jmmourier/laughing-couscous/software/applications/couscous/src/CouscousManager.cpp

#include "CouscousManager.h"

#include <atomic>
#include <chrono>
#include <cmath>

#include "Action.h"
#include "IHali.h"
#include "IHaliListener.h"
#include "Posi.h"
#include "PositionOrientation.h"
#include "RobotState.h"

CouscousManager::CouscousManager(
    const std::shared_ptr<IHali> &hali,
    const std::shared_ptr<Posi> &posi,
    const std::shared_ptr<WebServer> &web_server,
    const std::shared_ptr<Navi> &navi,
    const std::shared_ptr<Missi> &missi)
    : hali_(hali),
      posi_(posi),
      navi_(navi),
      web_server_(web_server),
      missi_(missi),
      is_robot_ready_(false),
      pre_launch_test_done_(false),
      mission_finished_(false) {
    web_server_thread_ = std::thread([&] { web_server_->start(); });

    // this is temporary and shall be replaced by a a listener on the strart button on the robot
    missi_->actionHasBeenDone();
}

void CouscousManager::runPreLaunchTest() {
    std::this_thread::sleep_for(std::chrono::milliseconds(1000));
    hali_->setGrabber(GrabberState::grabberClose);
    std::this_thread::sleep_for(std::chrono::milliseconds(1000));
    hali_->setGrabber(GrabberState::grabberOpen);
    std::this_thread::sleep_for(std::chrono::milliseconds(1000));
}

void CouscousManager::onPositionChanged(const PositionOrientation &position_orientation) {
    if (!pre_launch_test_done_ || !is_robot_ready_) {
        return;
    }
    RobotState currentState = web_server_->getRobotState();

    navi_->setCurrentPosition(
        position_orientation.x_m_,
        position_orientation.y_m_,
        position_orientation.orientation_rad_);

    Action nextAction = missi_->getCurrentAction();
    web_server_->setRobotState(RobotState(
        position_orientation,
        currentState.battery_,
        currentState.is_grabber_open_,
        currentState.mission_started_at_,
        currentState.mission_ended_at_,
        nextAction.type));

    if (nextAction.arguments == "mission done" && mission_finished_ == false) {
        const auto now = std::chrono::system_clock::now();
        const auto end_mission_timestamp =
            std::chrono::duration_cast<std::chrono::seconds>(now.time_since_epoch()).count();

        web_server_->setRobotState(RobotState(
            currentState.position_orientation_,
            currentState.battery_,
            currentState.is_grabber_open_,
            currentState.mission_started_at_,
            end_mission_timestamp,
            currentState.current_action_));
        mission_finished_ = true;
    }

    if (nextAction.type == WAIT) {
        std::cout << "[Missi]:wait" << std::endl;
        // wait timeout or mission is not started or mission is done
    } else if (nextAction.type == MOVE) {
        std::cout << "[Missi]:move" << nextAction.target_x << " " << nextAction.target_y
                  << std::endl;
        if (!nextAction.hasActionStarted) {
            navi_->setTargetPosition(nextAction.target_x, nextAction.target_y, 0);
        }
    } else if (nextAction.type == GRABBER) {
        std::cout << "[Missi]:grabber  : " << nextAction.grabber_state << std::endl;
        // define how this is read
        IHaliListener::GrabberState grabber_state = (nextAction.grabber_state.compare("open") == 0)
                                                        ? IHaliListener::GrabberState::grabberOpen
                                                        : IHaliListener::GrabberState::grabberClose;
        if (hali_->getGrabber() != grabber_state) {
            hali_->setGrabber(grabber_state);
        }
    } else if (nextAction.type == TURN) {
        std::cout << "[Missi]:turning " << nextAction.angle << std::endl;
        // TODO this need to be implemented
        if (!nextAction.hasActionStarted) {
            navi_->setTargetOrientation(nextAction.angle);
        }
    } else if (nextAction.type == MOVE_BACKWARD) {
        std::cout << "[Missi]:moving backward: " << nextAction.backward_distance << std::endl;
        if (!nextAction.hasActionStarted) {
            navi_->setBackwardDistance(nextAction.backward_distance);
        }
    } else if (nextAction.type == MOVE_FORWARD) {
        std::cout << "[Missi]:moving forward: " << nextAction.forward_distance << std::endl;
        if (!nextAction.hasActionStarted) {
            navi_->setForwardDistance(nextAction.forward_distance);
        }
    } else if (nextAction.type == UNKNOWN) {
        std::cout << "[Missi]:unknow action" << missi_->actionTypeToString(nextAction.type)
                  << std::endl;
        // This is abnormal, let's skip to next action
        missi_->actionHasBeenDone();
    }

    nextAction.hasActionStarted = true;
}

void CouscousManager::onWebServerPositionRequest(const PositionOrientation &position_orientation) {
    posi_->setPosition(position_orientation);
}

void CouscousManager::onWebServerSpeedRequest(const int &speed_motor1, const int &speed_motor2) {
    std::cout << "speed" << speed_motor1 << " " << speed_motor2 << std::endl;
    hali_->setMd25Speed(speed_motor1, speed_motor2);
}

// webserver send target position
void CouscousManager::onWebServerTargetPositionRequest(const double &pos_x, const double &pos_y) {
    navi_->setTargetPosition(pos_x, pos_y, 0);
}

// webserver send target rotation
void CouscousManager::onWebServerTargetOrientationRequest(const float &orientation_rad) {
    navi_->setTargetOrientation(orientation_rad);
};

void CouscousManager::onGrabberStateChanged(const GrabberState &graberState) {
    RobotState currentState = web_server_->getRobotState();
    web_server_->setRobotState(RobotState(
        currentState.position_orientation_,
        currentState.battery_,
        graberState == GrabberState::grabberOpen,
        currentState.mission_started_at_,
        currentState.mission_ended_at_,
        currentState.current_action_));
};

void CouscousManager::onNaviTargetReachedRequest(void) {
    Action current_action = missi_->getCurrentAction();
    if (current_action.type == MOVE || current_action.type == TURN ||
        current_action.type == MOVE_BACKWARD || current_action.type == MOVE_FORWARD) {
        missi_->actionHasBeenDone();
    }
}

// void CouscousManager::onNaviSpeedRequest(const int &speed_motor1, const int &speed_motor2) {
void CouscousManager::onNaviSpeedRequest(
    const float &v_x_mps,
    const float &v_y_mps,
    const float &omega_radps) {
    MotorSpeed motor_speed =
        moti_.getMotorSpeedFromBaseSpeed(BaseSpeed(v_x_mps, v_y_mps, omega_radps));
    hali_->setMd25Speed(motor_speed.speed_motor_1_, motor_speed.speed_motor_2_);
}

void CouscousManager::start() {
    hali_thread_ = std::thread([&] { hali_->updater(); });

    long rounds = 0;

    while (true) {
        if (is_robot_ready_) {
            auto encoders_motor1 = hali_->getEncoder(MotorIdEnum::motor1);
            auto encoders_motor2 = hali_->getEncoder(MotorIdEnum::motor2);

            posi_->updatePosition(encoders_motor1, encoders_motor2);

            if (rounds % (INTERVAL_REFRESH_BATTERY_MS / INTERVAL_REFRESH_MS) == 0) {
                RobotState currentState = web_server_->getRobotState();
                web_server_->setRobotState(RobotState(
                    currentState.position_orientation_,
                    static_cast<float>(hali_->getBatteryVoltage()) / 10,
                    currentState.is_grabber_open_,
                    currentState.mission_started_at_,
                    currentState.mission_ended_at_,
                    currentState.current_action_));
            }

            rounds++;
        } else if (!pre_launch_test_done_) {
            runPreLaunchTest();
            pre_launch_test_done_ = true;
        } else if (pre_launch_test_done_ && hali_->isRobotStarted()) {
            IHaliListener::RobotColor robot_color =
                hali_->getSwitch(SwitchId::switch1) ? RobotColor::YELLOW : RobotColor::BLUE;

            // Setting mission file according to robot's color
            std::string mission_file = std::string(std::getenv("MISSION_PATH")).append("/");
            missi_->setMissionFilePath(
                robot_color == RobotColor::YELLOW ? mission_file.append("mission_yellow.json")
                                                  : mission_file.append("mission_blue.json"));

            // note : the file mission.json shall be present on the same path the app is executed
            missi_->loadMissionFile();

            // Setting starting position according to robot's color
            auto starting_position = robot_color == RobotColor::YELLOW
                                         ? PositionOrientation(2.8, 1.2, M_PI)
                                         : PositionOrientation(0.2, 1.2, 0);

            const auto now = std::chrono::system_clock::now();
            const auto start_mission_timestamp =
                std::chrono::duration_cast<std::chrono::seconds>(now.time_since_epoch()).count();

            RobotState currentState = web_server_->getRobotState();
            web_server_->setRobotState(RobotState(
                currentState.position_orientation_,
                currentState.battery_,
                currentState.is_grabber_open_,
                start_mission_timestamp,
                currentState.mission_ended_at_,
                currentState.current_action_));

            posi_->setPosition(starting_position);

            is_robot_ready_ = true;
        }

        std::this_thread::sleep_for(std::chrono::milliseconds(INTERVAL_REFRESH_MS));
    }
    web_server_thread_.join();
    hali_thread_.join();
}
