jmmourier/laughing-couscous/software/modules/navi/src/Navi.cpp

#include "Navi.h"

#include <spdlog/logger.h>

#include <cmath>
#include <iostream>

#include "NaviUtils.h"
#include "logger/LoggerFactory.h"

#define TARGET_REACHED_DISTANCE 0.007
#define TARGET_ANGLE_REACHED_RAD 0.02
#define MAX_ROTATION 0.85
#define ANGLE_FOR_ROTATION_ONLY_RAD 0.07
#define MAX_SPEED 0.5
#define SLOW_MOVE_SPEED 0.10
#define SIM_SPEED_FACTOR 2
Navi::Navi()
    : logger_(LoggerFactory::registerOrGetLogger("Navi", spdlog::level::level_enum::info)) {}

void Navi::registerNaviRequestListener(const std::weak_ptr<INaviRequestListener> &navi_listener) {
    navi_listeners_.push_back(navi_listener);
}

// void Navi::publishToNaviSpeedRequestListeners(const int &motor1, const int &motor2) const {
void Navi::publishToNaviSpeedRequestListeners(
    const float &v_x_mps,
    const float &v_y_mps,
    const float &omega_radps) const {
    for (auto const &navi_listener_ptr : navi_listeners_) {
        if (auto navi_listener = navi_listener_ptr.lock()) {
            navi_listener->onNaviSpeedRequest(v_x_mps, v_y_mps, omega_radps);
        }
    }
}

void Navi::publishToNaviTargetReachedListeners(void) const {
    for (auto const &navi_listener_ptr : navi_listeners_) {
        if (auto navi_listener = navi_listener_ptr.lock()) {
            navi_listener->onNaviTargetReachedRequest();
        }
    }
}

int Navi::setTargetPosition(
    const double &target_pos_x,
    const double &target_pos_y,
    const double &target_orientation) {
    target_position_.pos_x = target_pos_x;
    target_position_.pos_y = target_pos_y;
    target_position_.orientation = target_orientation;
    action_in_progress_ = position;
    SPDLOG_LOGGER_INFO(logger_, "[Navi] set target position x:{} y:{}", target_pos_x, target_pos_y);
    return 0;
}

int Navi::setTargetOrientation(const float &orientation_rad) {
    target_position_.orientation = orientation_rad;

    action_in_progress_ = rotation;
    SPDLOG_LOGGER_INFO(logger_, "[Navi] set orientation {}rad", orientation_rad);
    return 0;
}

int Navi::setBackwardDistance(const double &dist) {
    if (action_in_progress_ != backward) {
        backward_dist_ = dist;
        current_pos_before_backward_move_.pos_x = actual_robot_position_.pos_x;
        current_pos_before_backward_move_.pos_y = actual_robot_position_.pos_y;
        action_in_progress_ = backward;
        SPDLOG_LOGGER_INFO(logger_, "[Navi] set backward position dist:{}", backward_dist_);
    }
    return 0;
}

int Navi::setForwardDistance(const double &dist) {
    if (action_in_progress_ != forward) {
        forward_dist_ = dist;
        current_pos_before_forward_move_.pos_x = actual_robot_position_.pos_x;
        current_pos_before_forward_move_.pos_y = actual_robot_position_.pos_y;
        action_in_progress_ = forward;
        SPDLOG_LOGGER_INFO(logger_, "[Navi] set forward position dist:{}", forward_dist_);
    }
    return 0;
}

int Navi::setCurrentPosition(
    const double &new_rob_pos_x,
    const double &new_rob_pos_y,
    const double &new_rob_orientation) {
    actual_robot_position_.pos_x = new_rob_pos_x;
    actual_robot_position_.pos_y = new_rob_pos_y;
    actual_robot_position_.orientation = new_rob_orientation;
    switch (action_in_progress_) {
        case idle:
            break;
        case position:
            computeRegulatorSpeed(actual_robot_position_, target_position_);
            break;
        case rotation:
            computeRotationSpeed(new_rob_orientation, target_position_.orientation);
            break;
        case backward:
            computeBackwardSpeed(actual_robot_position_, current_pos_before_backward_move_);
            break;
        case forward:
            computeForwardSpeed(actual_robot_position_, current_pos_before_forward_move_);
    }
    return 0;
}

void Navi::computeRegulatorSpeed(const pos_info &robot_pos, const pos_info &target_pos) {
    // std::cout << "compute speed" << std::endl;
    double distance = getDistanceToTarget(robot_pos, target_pos);
    double rotation, speed = 0;
    // hasPositionBeenReached
    if (std::abs(distance) < TARGET_REACHED_DISTANCE) {
        rotation = 0;
        speed = 0;
        publishToNaviSpeedRequestListeners(0, 0, 0);
        publishToNaviTargetReachedListeners();
        action_in_progress_ = idle;
        SPDLOG_LOGGER_INFO(logger_, "[Navi] target reached");
        return;
    }

    // cap regulation
    double errorCap = shortcut_getAngleToTarget(robot_pos, target_pos);

    if (errorCap > M_PI) {
        errorCap = errorCap - (2 * M_PI);
    }
    if (errorCap < -M_PI) {
        errorCap = errorCap + (2 * M_PI);
    }

    rotation = 1.2*errorCap;
    if (rotation > MAX_ROTATION) rotation = MAX_ROTATION;
    if (rotation < -MAX_ROTATION) rotation = -MAX_ROTATION;

    // Speed regulation
    if (std::abs(errorCap) > ANGLE_FOR_ROTATION_ONLY_RAD) {
        SPDLOG_LOGGER_INFO(logger_, "[Navi] error cap:{}rad", errorCap);
        speed = 0;
    } else {
        speed = distance;
        SPDLOG_LOGGER_INFO(logger_, "[Navi] update dist:{} error cap:{} rad", distance, errorCap);
        if (speed > MAX_SPEED) speed = MAX_SPEED;
    }

    publishToNaviSpeedRequestListeners(speed, 0, rotation);
}

void Navi::computeRotationSpeed(const double robot_orientation, const double target_orientation) {
    // double errorCap = std::abs(robot_orientation - target_orientation);
    double errorCap = getAngleBetweenTwoAngles(robot_orientation, target_orientation);
    if (std::abs(errorCap) < TARGET_ANGLE_REACHED_RAD) {
        SPDLOG_LOGGER_INFO(logger_, "[Navi] angle reached");
        publishToNaviSpeedRequestListeners(0, 0, 0);
        publishToNaviTargetReachedListeners();
        action_in_progress_ = idle;
        return;
    }

    if (errorCap > M_PI) {
        errorCap = errorCap - (2 * M_PI);
    }
    if (errorCap < -M_PI) {
        errorCap = errorCap + (2 * M_PI);
    }

    double rotation = 1.2 * errorCap;
    if (rotation > MAX_ROTATION) rotation = MAX_ROTATION;
    if (rotation < -MAX_ROTATION) rotation = -MAX_ROTATION;

    publishToNaviSpeedRequestListeners(0, 0, rotation);
    /*rotdir rotation_direction = getRotationDir(robot_orientation, target_orientation);
    if (rotation_direction == rotdir::Clockwise) {
        SPDLOG_LOGGER_INFO(logger_, "[Navi] rotate clockwise :{}", rotation);
        publishToNaviSpeedRequestListeners(0, 0, rotation);
    } else {
        SPDLOG_LOGGER_INFO(logger_, "[Navi] rotate anti-clockwise :{} ", rotation);
        publishToNaviSpeedRequestListeners(0, 0, rotation);
    }*/
    SPDLOG_LOGGER_INFO(
        logger_,
        "[Navi] robot orientation:{} error cap:{}rad ",
        robot_orientation,
        errorCap);
}

void Navi::computeBackwardSpeed(
    const pos_info &current_robot_pos,
    const pos_info &previous_robot_pos) {
    double distance_to_target = getDistanceToTarget(current_robot_pos, previous_robot_pos);
    double speed = 0;
    SPDLOG_LOGGER_INFO(
        logger_,
        "[Navi] moving backward dist:{} posX:{} posY:{}",
        getDistanceToTarget(current_robot_pos, previous_robot_pos),
        current_robot_pos.pos_x,
        current_robot_pos.pos_y);
    if (std::abs(distance_to_target) > std::abs(backward_dist_ - TARGET_REACHED_DISTANCE)) {
        speed = 0;
        publishToNaviSpeedRequestListeners(0, 0, 0);
        publishToNaviTargetReachedListeners();
        action_in_progress_ = idle;
        SPDLOG_LOGGER_INFO(logger_, "[Navi] target reached");
        return;
    }

    publishToNaviSpeedRequestListeners(-SLOW_MOVE_SPEED, 0, 0);
}

void Navi::computeForwardSpeed(
    const pos_info &current_robot_pos,
    const pos_info &previous_robot_pos) {
    double distance_to_target = getDistanceToTarget(current_robot_pos, previous_robot_pos);
    double speed = 0;
    SPDLOG_LOGGER_INFO(
        logger_,
        "[Navi] moving forward dist:{} posX:{} posY:{}",
        getDistanceToTarget(current_robot_pos, previous_robot_pos),
        current_robot_pos.pos_x,
        current_robot_pos.pos_y);
    if (std::abs(distance_to_target) > std::abs(forward_dist_ - TARGET_REACHED_DISTANCE)) {
        speed = 0;
        publishToNaviSpeedRequestListeners(0, 0, 0);
        publishToNaviTargetReachedListeners();
        action_in_progress_ = idle;
        SPDLOG_LOGGER_INFO(logger_, "[Navi] target reached");
        return;
    }

    publishToNaviSpeedRequestListeners(SLOW_MOVE_SPEED, 0, 0);
}
