jmmourier/laughing-couscous/software/modules/navi/include/INaviRequestListener.h

#ifndef INAVIREQUESTLISTENER_H
#define INAVIREQUESTLISTENER_H

class INaviRequestListener {
   public:
    // virtual void onNaviSpeedRequest(const int &motor1, const int &motor2) = 0;
    virtual void
    onNaviSpeedRequest(const float &v_x_mps, const float &v_y_mps, const float &omega_radps) = 0;
    virtual void onNaviTargetReachedRequest(void) = 0;
};

#endif  // INAVIREQUESTLISTENER_H
