jmmourier/laughing-couscous/software/modules/navi/src/NaviRegulator.cpp

#include "NaviRegulator.h"

#include <iostream>

#include "logger/LoggerFactory.h"

int NaviRegulator::setCurrentPosition(
    const double &new_rob_pos_x,
    const double &new_rob_pos_y,
    const double &new_rob_orientation) {}
