jmmourier/laughing-couscous/software/modules/hali/include/CommandInterpreter.h

#ifndef HALI_COMMAND_INTERPRETER_H
#define HALI_COMMAND_INTERPRETER_H

class CommandInterpreter {
   public:
    CommandInterpreter(/* args */);

   private:
    /* data */
};

#endif  // HALI_COMMAND_INTERPRETER_H
