jmmourier/laughing-couscous/software/application_test_gui/src/main.cpp

#include <iostream>
#include <memory>

#include "CouscousManager.h"
#include "HalSimu.h"
#include "Posi.h"
#include "RealTime.h"
#include "WebServer.h"

int main(int argc, char *argv[]) {
    auto couscousManager = std::make_shared<CouscousManager>(std::make_shared<HalSimu>());
    couscousManager->start();

    return 0;
}
