jmmourier/laughing-couscous/software/modules/gui/include/WebServer.h

#ifndef WEB_SERVER_H
#define WEB_SERVER_H

#include "IWebServerRequestListener.h"
#include "PositionOrientation.h"
#include "RobotState.h"
#include "Types.h"
#include "WebPositionService.h"
#include "grpcpp/server.h"

class WebServer {
   public:
    void registerWebServerRequestListener(
        const std::weak_ptr<IWebServerRequestListener> &webserver_listener);
    /**
     * @brief Create and launch web server and it's services
     *
     */
    void start();

    /**
     * @brief Shutsdown web server
     *
     */
    void stop();

    void setRobotState(const RobotState &robot_state);
    RobotState getRobotState();

   private:
    std::shared_ptr<grpc::Server> server_;
    WebPositionService web_position_service_;
};

#endif  // WEB_SERVER_H
